kgl2001/RiscPC_A7000_Econet_Podule/KiCAD Files/3DModels/SSW-117-01-T-S.stp

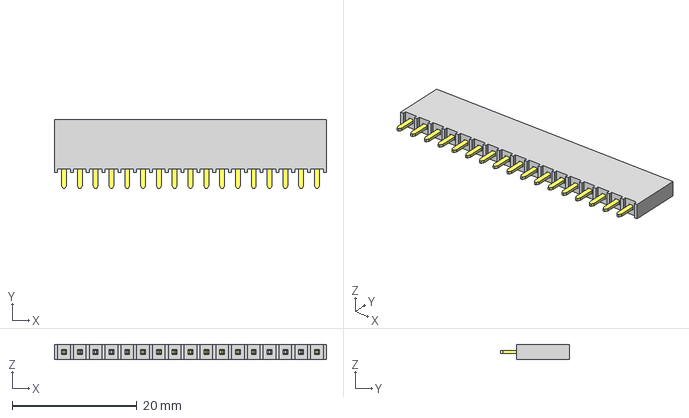
[picture p11: CAD file, 2023-10-07]
KiCAD Files/3DModels/SSW-117-01-T-S.stp
43.7 x 11.2 x 2.41 mm
P2SSW-117-01-T-S
T1SSW-117-01-T-S
