kgl2001/RiscPC_A7000_Econet_Podule/KiCAD Files/3DModels/User Library-DIN-5.STEP

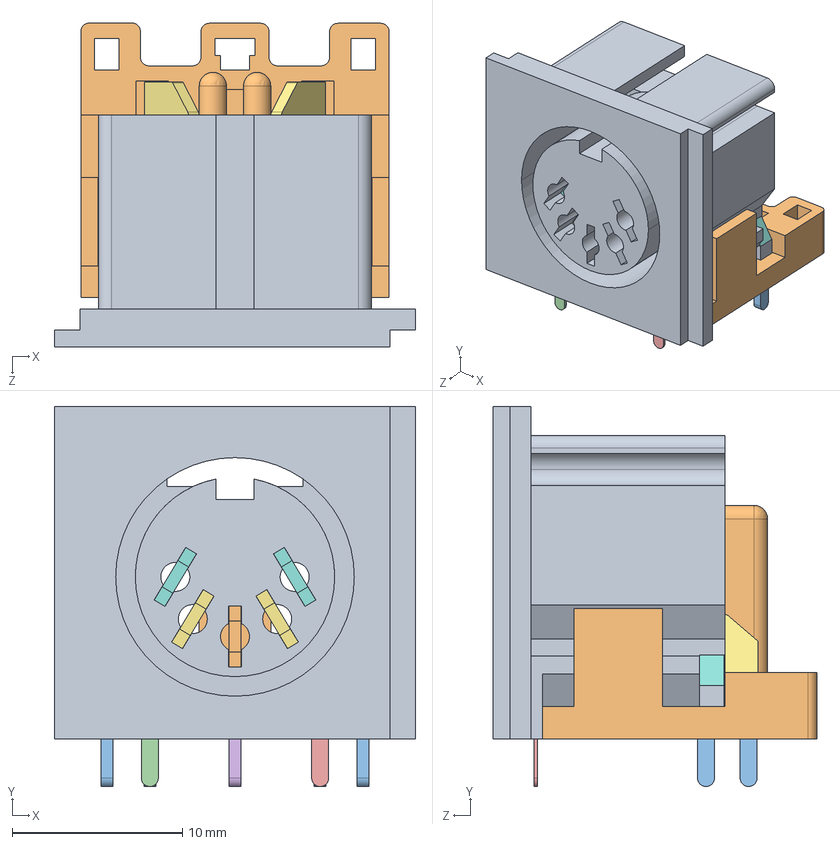
[picture p12: CAD file, 2023-10-07]
KiCAD Files/3DModels/User Library-DIN-5.STEP
21.2 x 22.3 x 19.0 mm
DIN5 A
DIN5 B
DIN5 C
DIN D x 2
DIN E x 2
DIN EE x 2
DIN G
DIN DD x 2
