kgl2001/RiscPC_A7000_Econet_Podule/KiCAD Files/3DModels/SSW-120-06-F-D.stp

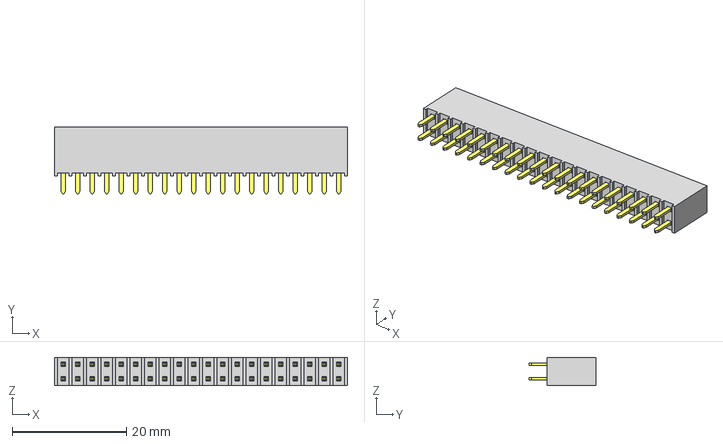
[picture p13: CAD file, 2023-10-07]
KiCAD Files/3DModels/SSW-120-06-F-D.stp
51.3 x 11.7 x 4.95 mm
_T1SSW-120-06-F-D
_P2SSW-120-06-F-D
