kgl2001/RiscPC_A7000_Econet_Podule/KiCAD Files/3DModels/DIN5_PCB_DELTRON_671-0500.STEP

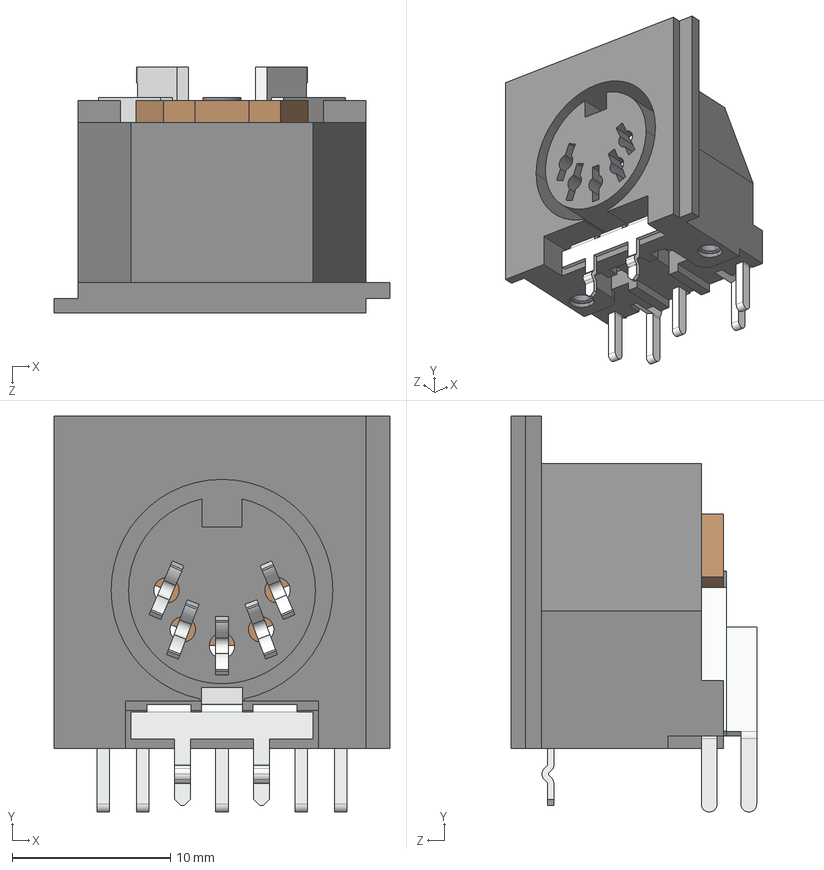
[picture p14: CAD file, 2023-10-07]
KiCAD Files/3DModels/DIN5_PCB_DELTRON_671-0500.STEP
21.2 x 25.0 x 15.5 mm
DIN5_PCB_DELTRON_BODY
DIN5_PCB_DELTRON_PIN2
DIN5_PCB_DELTRON_PIN5
DIN5_PCB_DELTRON_PIN3
DIN5_PCB_DELTRON_PIN4
DIN5_PCB_DELTRON_PIN1
DIN5_PCB_DELTRON_FIX
DIN5_PCB_DELTRON_SHIELD
